CIRCUITSTATE/ESPNut-D1/Docs/Resources/ESPNut-D1-R0.1-PCB-Featured-Image-1-JPG-3-1.jpg

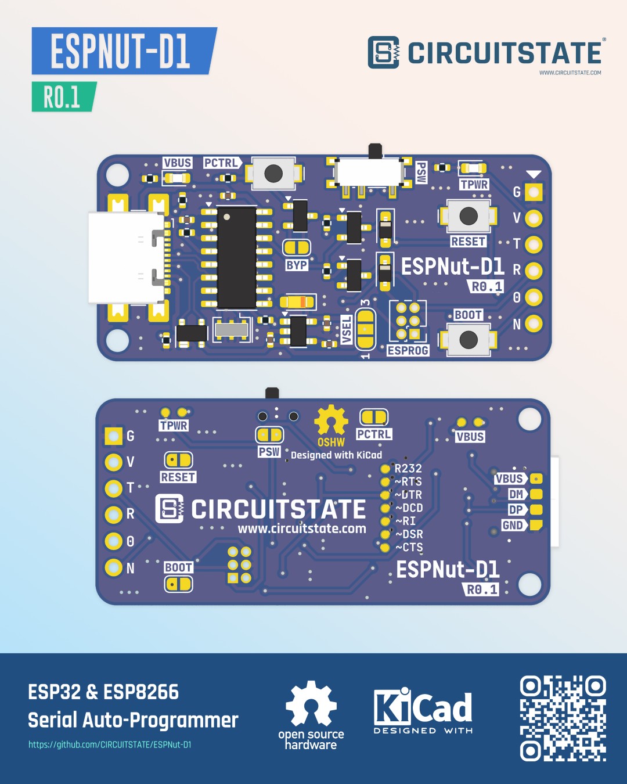
Docs/Resources/ESPNut-D1-R0.1-PCB-Featured-Image-1-JPG-3-1.jpg
