CIRCUITSTATE/ESPNut-D1/Export/R0.1/2025-04-23/Renders/ESPNut-D1-R0.1-PCB-Back-23042025-1.png

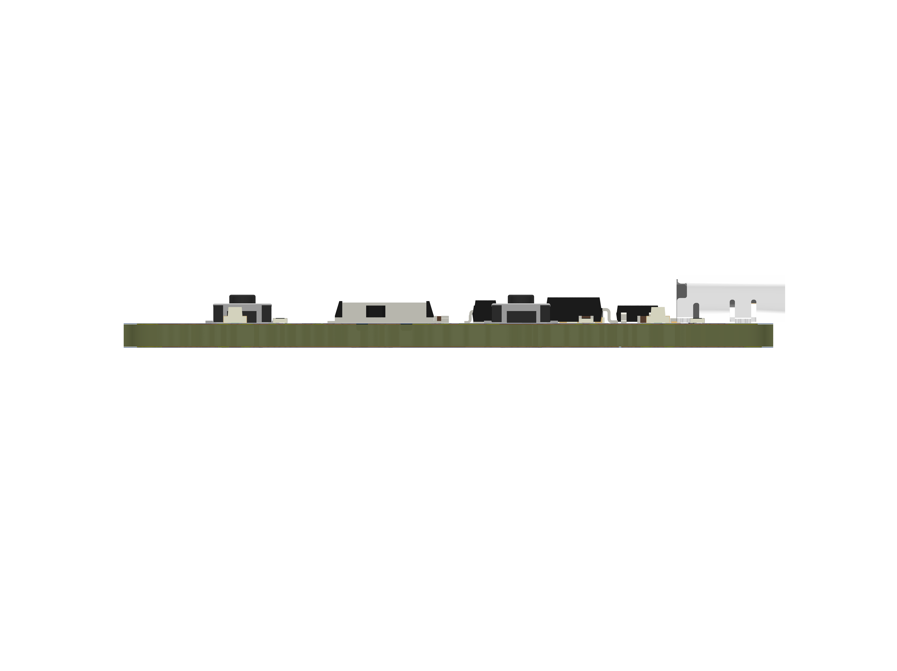
Export/R0.1/2025-04-23/Renders/ESPNut-D1-R0.1-PCB-Back-23042025-1.png
