CIRCUITSTATE/ESPNut-D1/Export/R0.3/2025-08-02/SCH/ESPNut-D1-R0.3-SCH-02082025-1_1.png

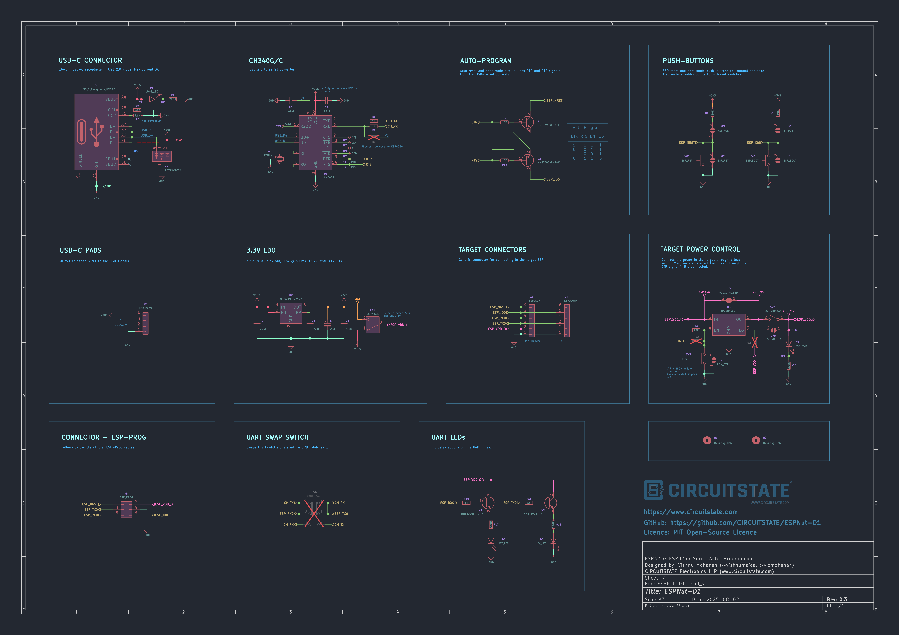
Export/R0.3/2025-08-02/SCH/ESPNut-D1-R0.3-SCH-02082025-1_1.png
