CIRCUITSTATE/ESPNut-D1/Export/R0.3/2025-10-25/Renders/ESPNut-D1-R0.3-PCB-Left-25102025-1-Cropped.png

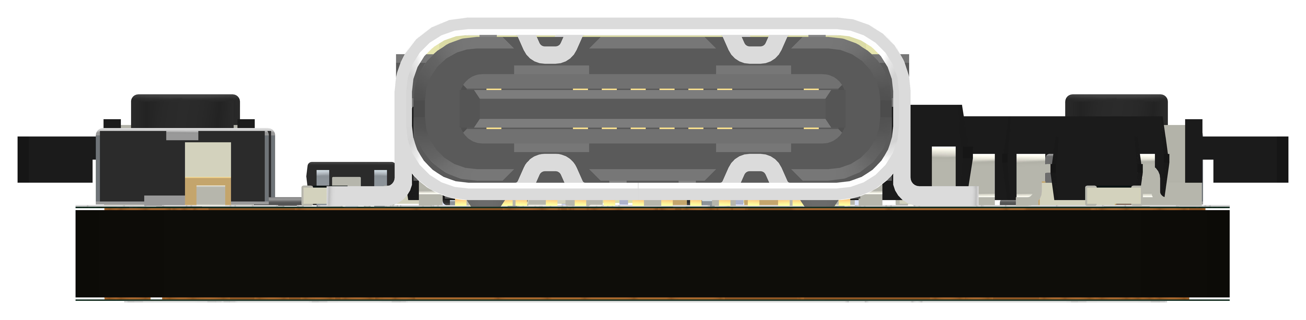
Export/R0.3/2025-10-25/Renders/ESPNut-D1-R0.3-PCB-Left-25102025-1-Cropped.png
