CIRCUITSTATE/ESPNut-D1/Export/R0.4/2025-11-07/Renders/ESPNut-D1-R0.4-PCB-Front-07112025-1-Cropped.png

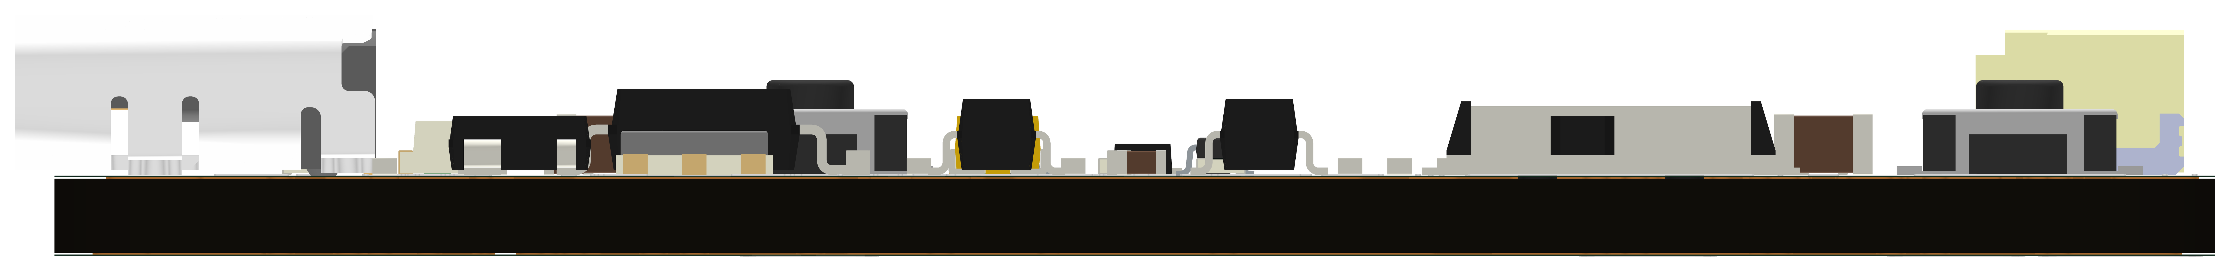
Export/R0.4/2025-11-07/Renders/ESPNut-D1-R0.4-PCB-Front-07112025-1-Cropped.png
