CIRCUITSTATE/ESPNut-D1/Export/R0.3/2025-10-23/Renders/ESPNut-D1-R0.3-PCB-Parts-Front-23102025-1.png

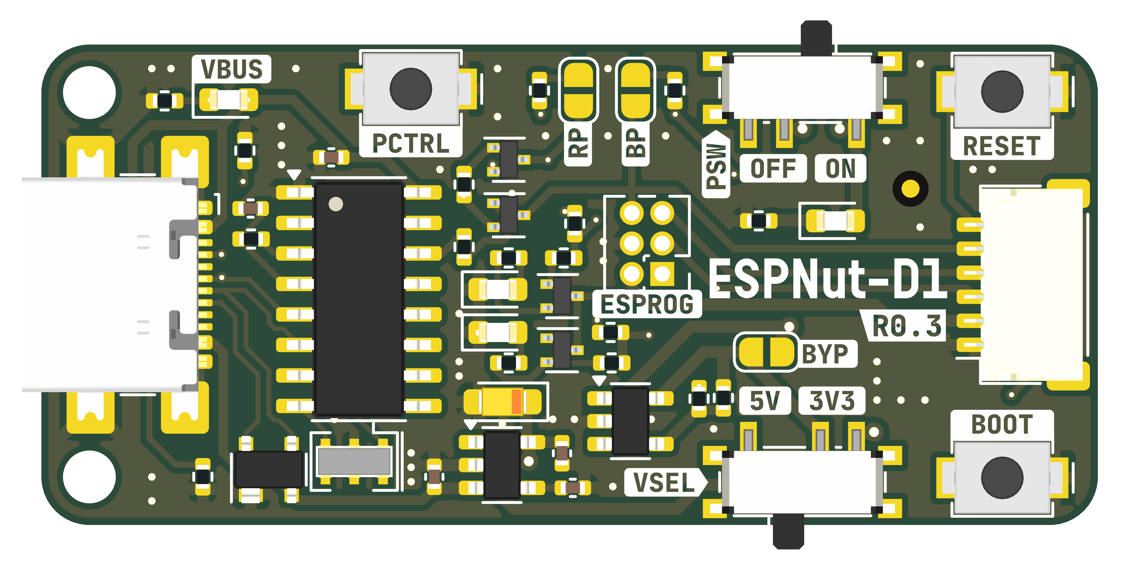
Export/R0.3/2025-10-23/Renders/ESPNut-D1-R0.3-PCB-Parts-Front-23102025-1.png
