CIRCUITSTATE/ESPNut-D1/Export/R0.4/2025-11-07/PCB/ESPNut-D1-R0.4-User_Comments.pdf

Castellated | pads: F.Mask Type | | Epsilon R | 0

0.035 mm | 1 Not specified
0 mm

4.5 | 0.02
