CIRCUITSTATE/ESPNut-D1/Export/R0.4/2025-11-07/SCH/ESPNut-D1-R0.4-SCH-07112025-1.pdf

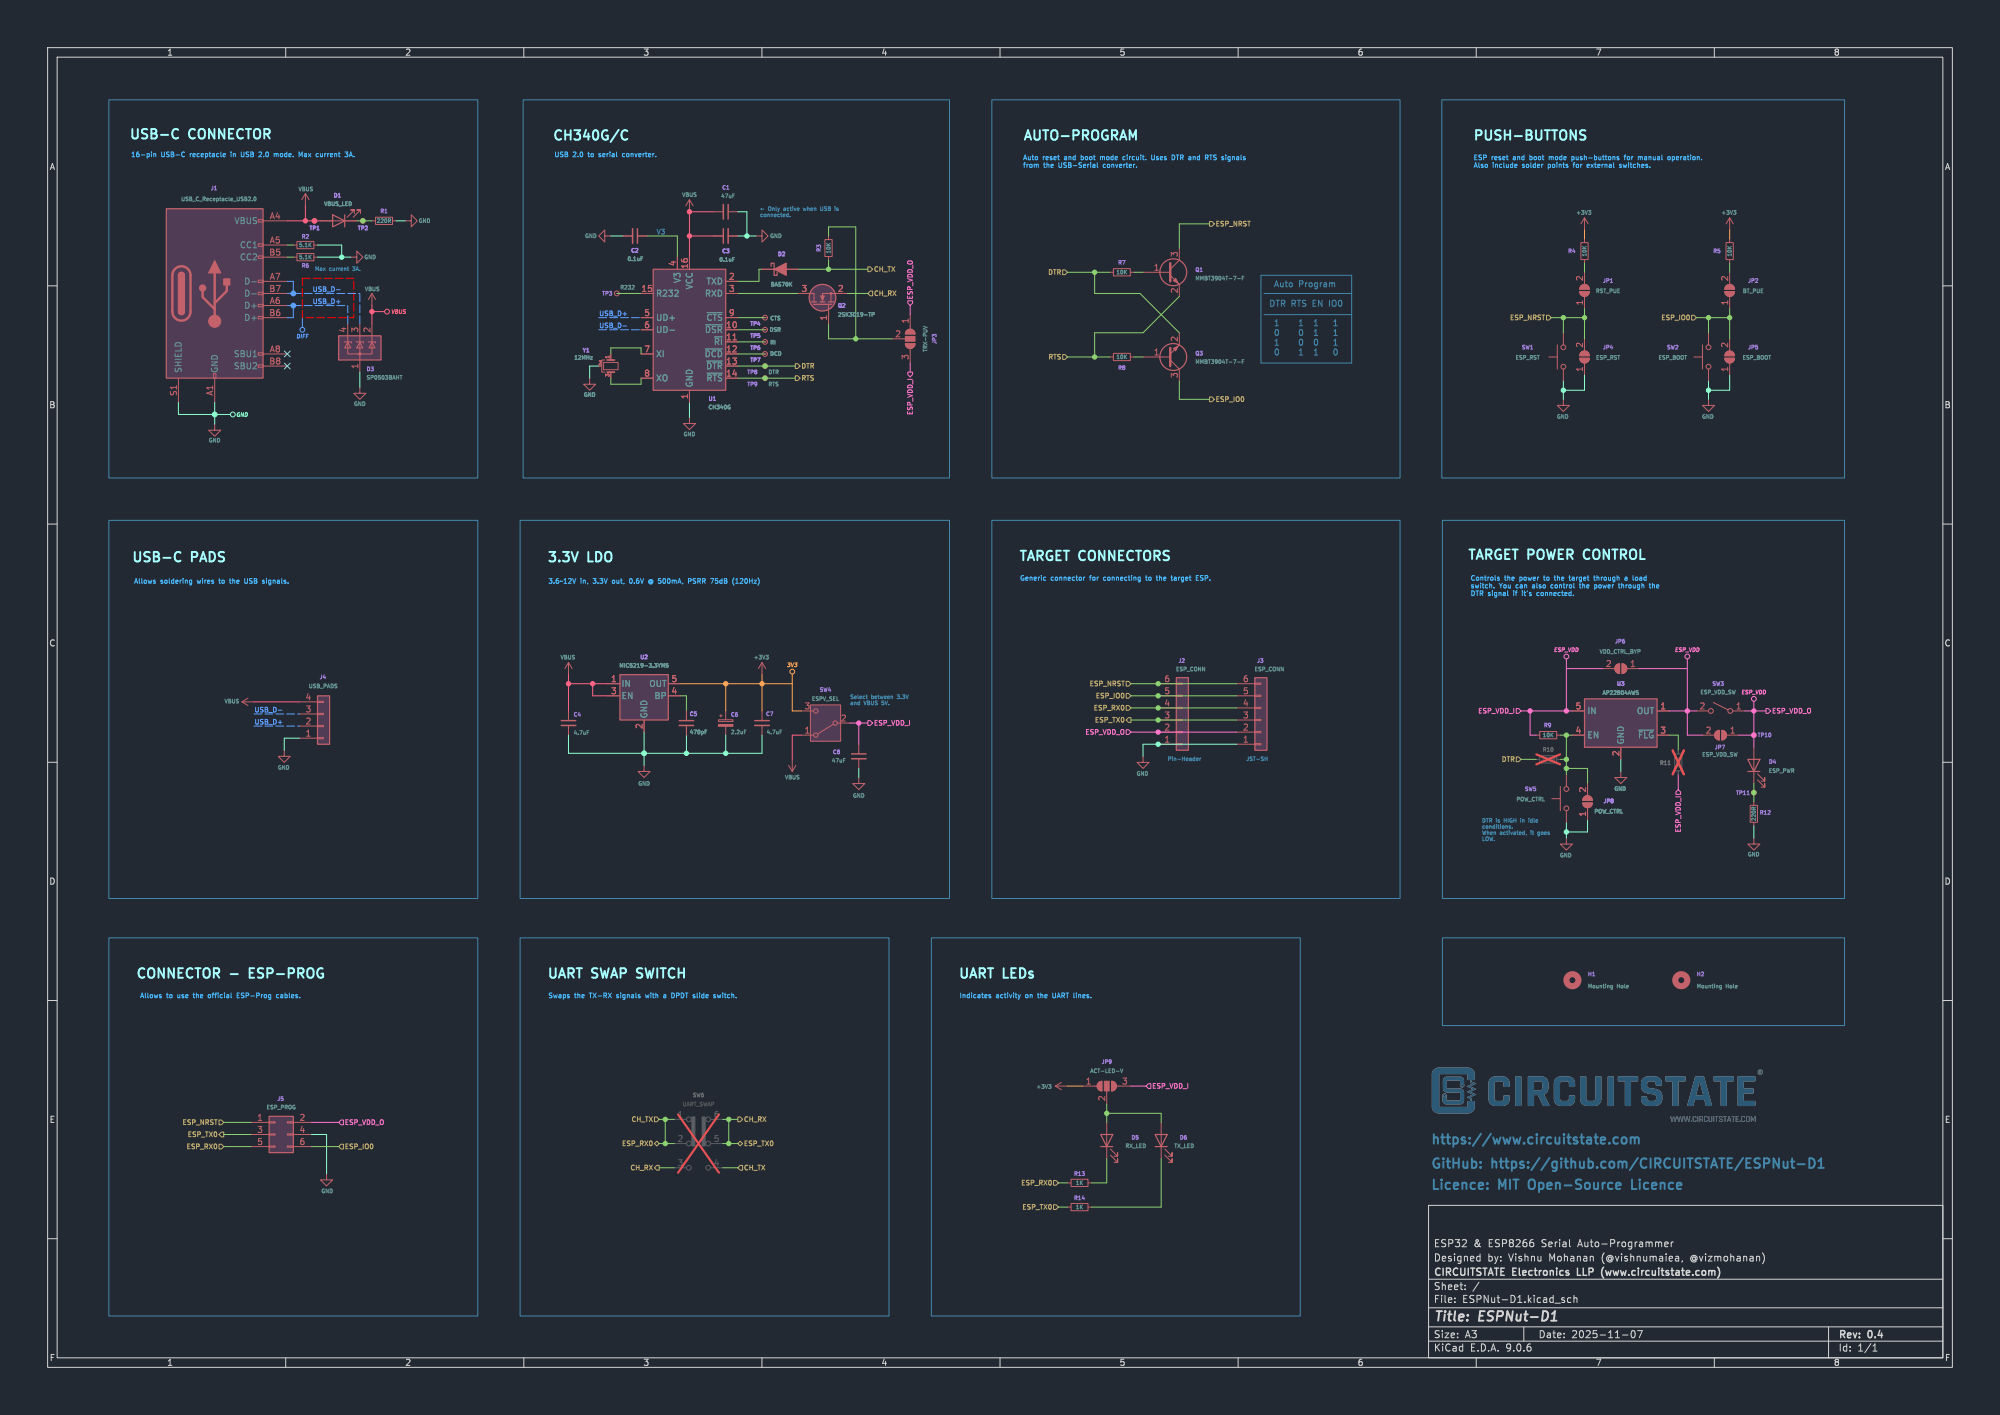
[picture p34: page 1]

þÿ!•Only active when USB is
connected.

1 TXD 2 RXD 3 ~{CTS}9 ~{DSR} 10 ~{RI} 11 ~{DCD} 12 ~{DTR} 13 ~{RTS} 14

and VBUS 5V. 3.6~12V in, 3.3V out, 0.6V @ 500mA, PSRR 75dB (120Hz)

https://www.circuitstate.com
