CIRCUITSTATE/ESPNut-D1/Export/R0.3/2025-10-25/PCB/ESPNut-D1-R0.3-PCB-PDF-All-25102025-1.pdf

D Date: 2025-08-02 KiCad; E.D.A. 9.0.5 Size: A4; Rev: 0.3; File: ESPNut-D1.kicad_pcb Sheet: CIRCUITSTATE; Electronics; LLP www.circuitstate.com; Designed; by: Vishnu; Mohanan (@vishnumaiea,; @vizmohanan) ESP32 &; ESP8266 Serial Auto-Programmer

Id: 1/1 Title: ESPNut-D1

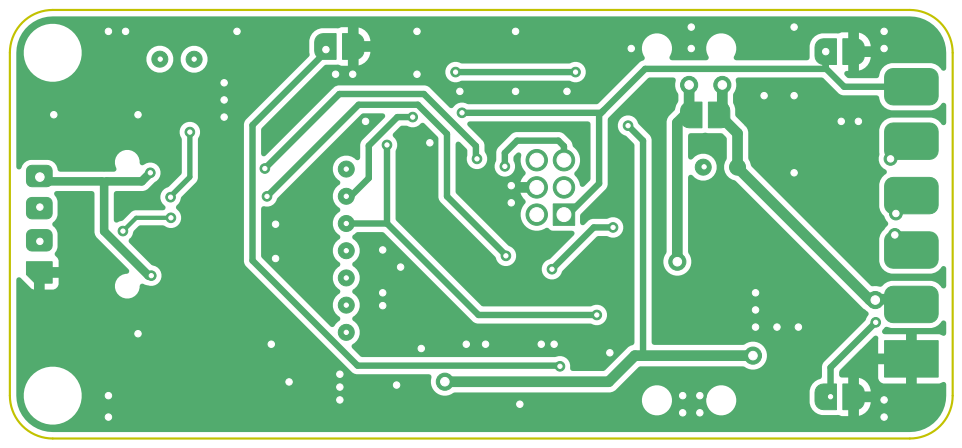
[picture p37: page 2]
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

Id: 1/1 Title: ESPNut-D1

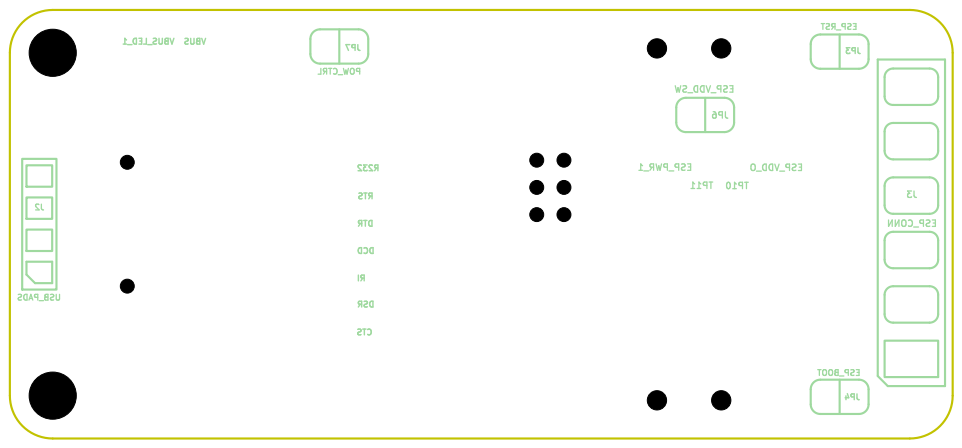
[picture p38: page 3]
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

Id: 1/1 Title: ESPNut-D1

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

Id: 1/1 Title: ESPNut-D1

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

Id: 1/1 Title: ESPNut-D1

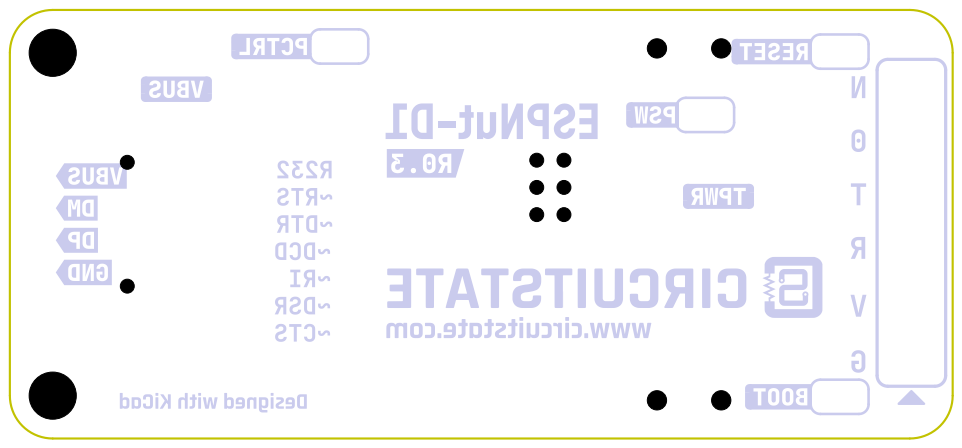
[picture p39: page 6]
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

Id: 1/1 Title: ESPNut-D1

Id: 1/1 Title: ESPNut-D1

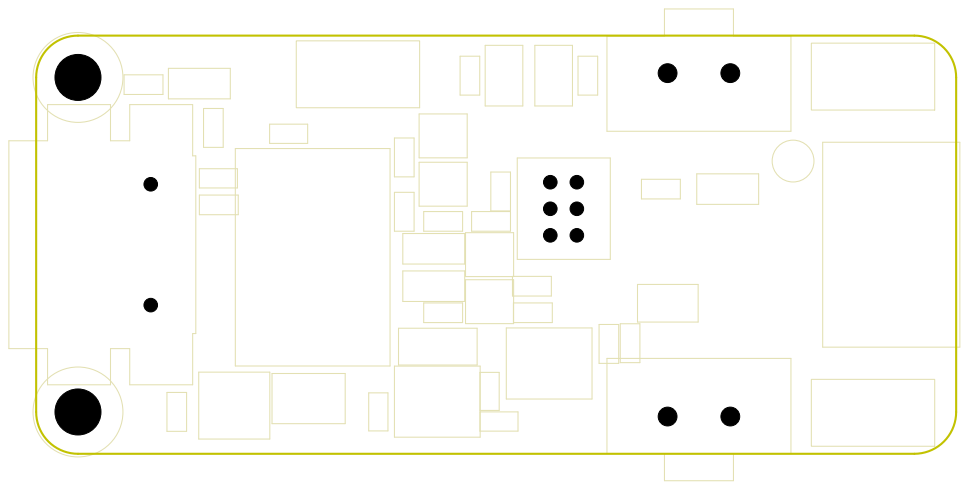
[picture p40: page 8]
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

Id: 1/1 Title: ESPNut-D1

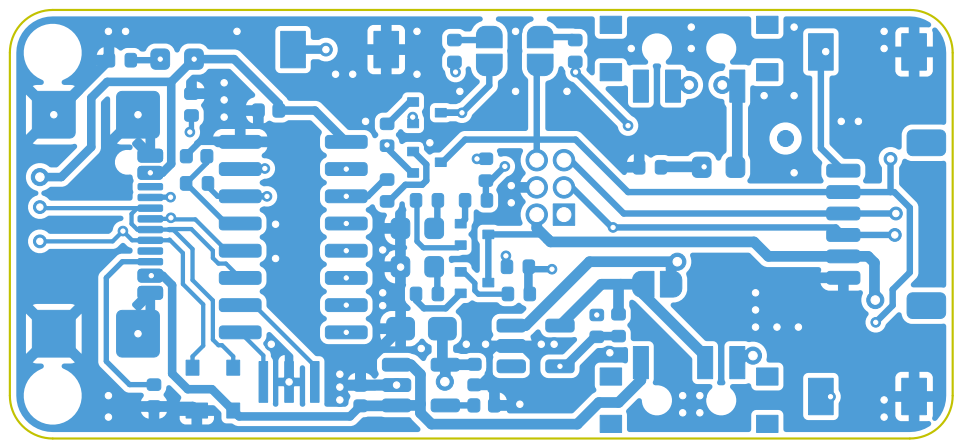
[picture p41: page 9]
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

Id: 1/1 Title: ESPNut-D1

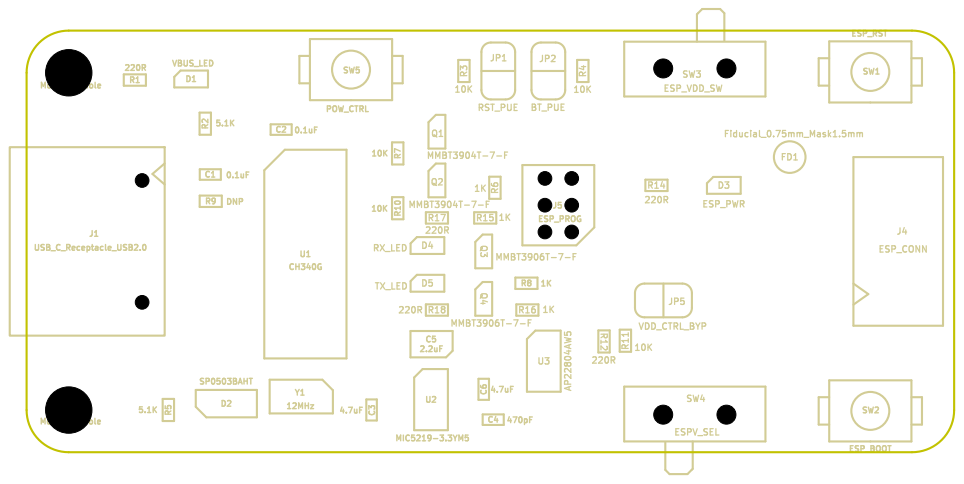
[picture p42: page 10]

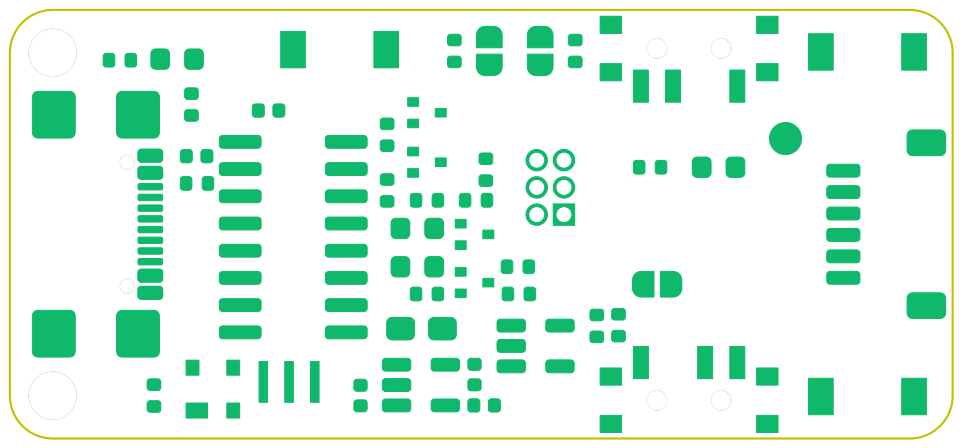
[picture p43: page 11]
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

Id: 1/1 Title: ESPNut-D1

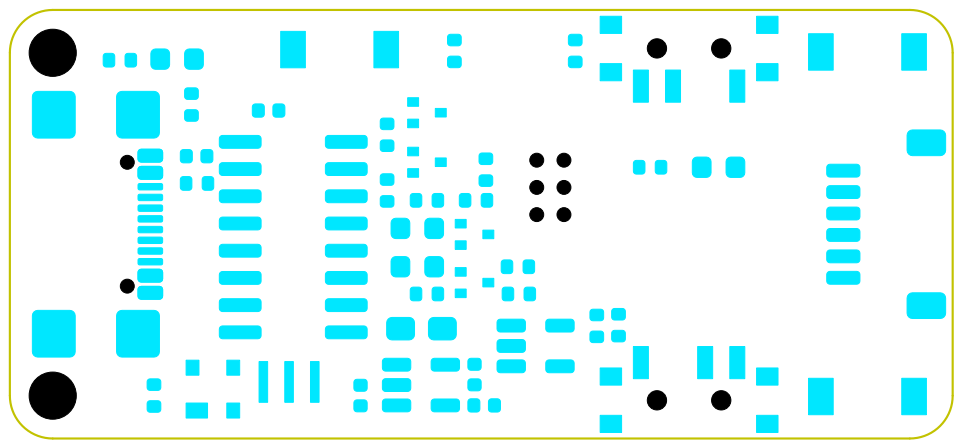
[picture p44: page 12]
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

Id: 1/1 Title: ESPNut-D1

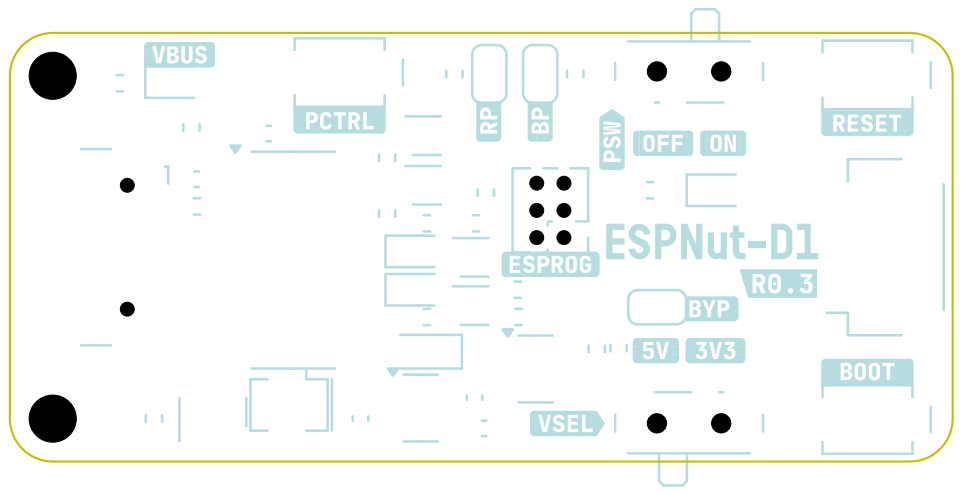
[picture p45: page 13]
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

Id: 1/1 Title: ESPNut-D1

D Date: 2025-08-02 KiCad; E.D.A. 9.0.5 Size: A4; Rev: 0.3; File: ESPNut-D1.kicad_pcb Sheet: CIRCUITSTATE; Electronics; LLP www.circuitstate.com; Designed; by: Vishnu; Mohanan (@vishnumaiea,; @vizmohanan) ESP32 &; ESP8266 Serial Auto-Programmer; BOARD CHARACTERISTICS; Board; overall; dimensions:; Not specified; Top Solder; PasteENIG; copper; F.Paste; Impedance; Control: 0.01; 0 Plated; Edge: F.Silkscreen B.Silkscreen Min track/spacing:; Thickness; (mm) Not specified; Loss Tangent Min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

Castellated | pads: F.Mask Type | | | | | | Epsilon R | 0

Layer Name Dielectric | Bottom Silk Screen Screen Bottom Solder Mask | | Not specified | 0.01 mm | | 3.3 Top Silk 3.3 1 Bottom Solder Paste 1 Not specified | 0 F.Cu

0 mm | | | 0
0 mm

0.035 mm | | 1 Not specified

4.5 | 0.02

Id: 1/1 Title: ESPNut-D1

D Date: 2025-08-02 KiCad; E.D.A. 9.0.5 Size: A4; Rev: 0.3; File: ESPNut-D1.kicad_pcb Sheet: CIRCUITSTATE; Electronics; LLP www.circuitstate.com; Designed; by: Vishnu; Mohanan (@vishnumaiea,; @vizmohanan) ESP32 &; ESP8266 Serial Auto-Programmer; PCB Edge

Id: 1/1 Title: ESPNut-D1
