CIRCUITSTATE/ESPNut-D1/Export/R0.3/2025-10-25/SCH/ESPNut-D1-R0.3-SCH-25102025-1.pdf

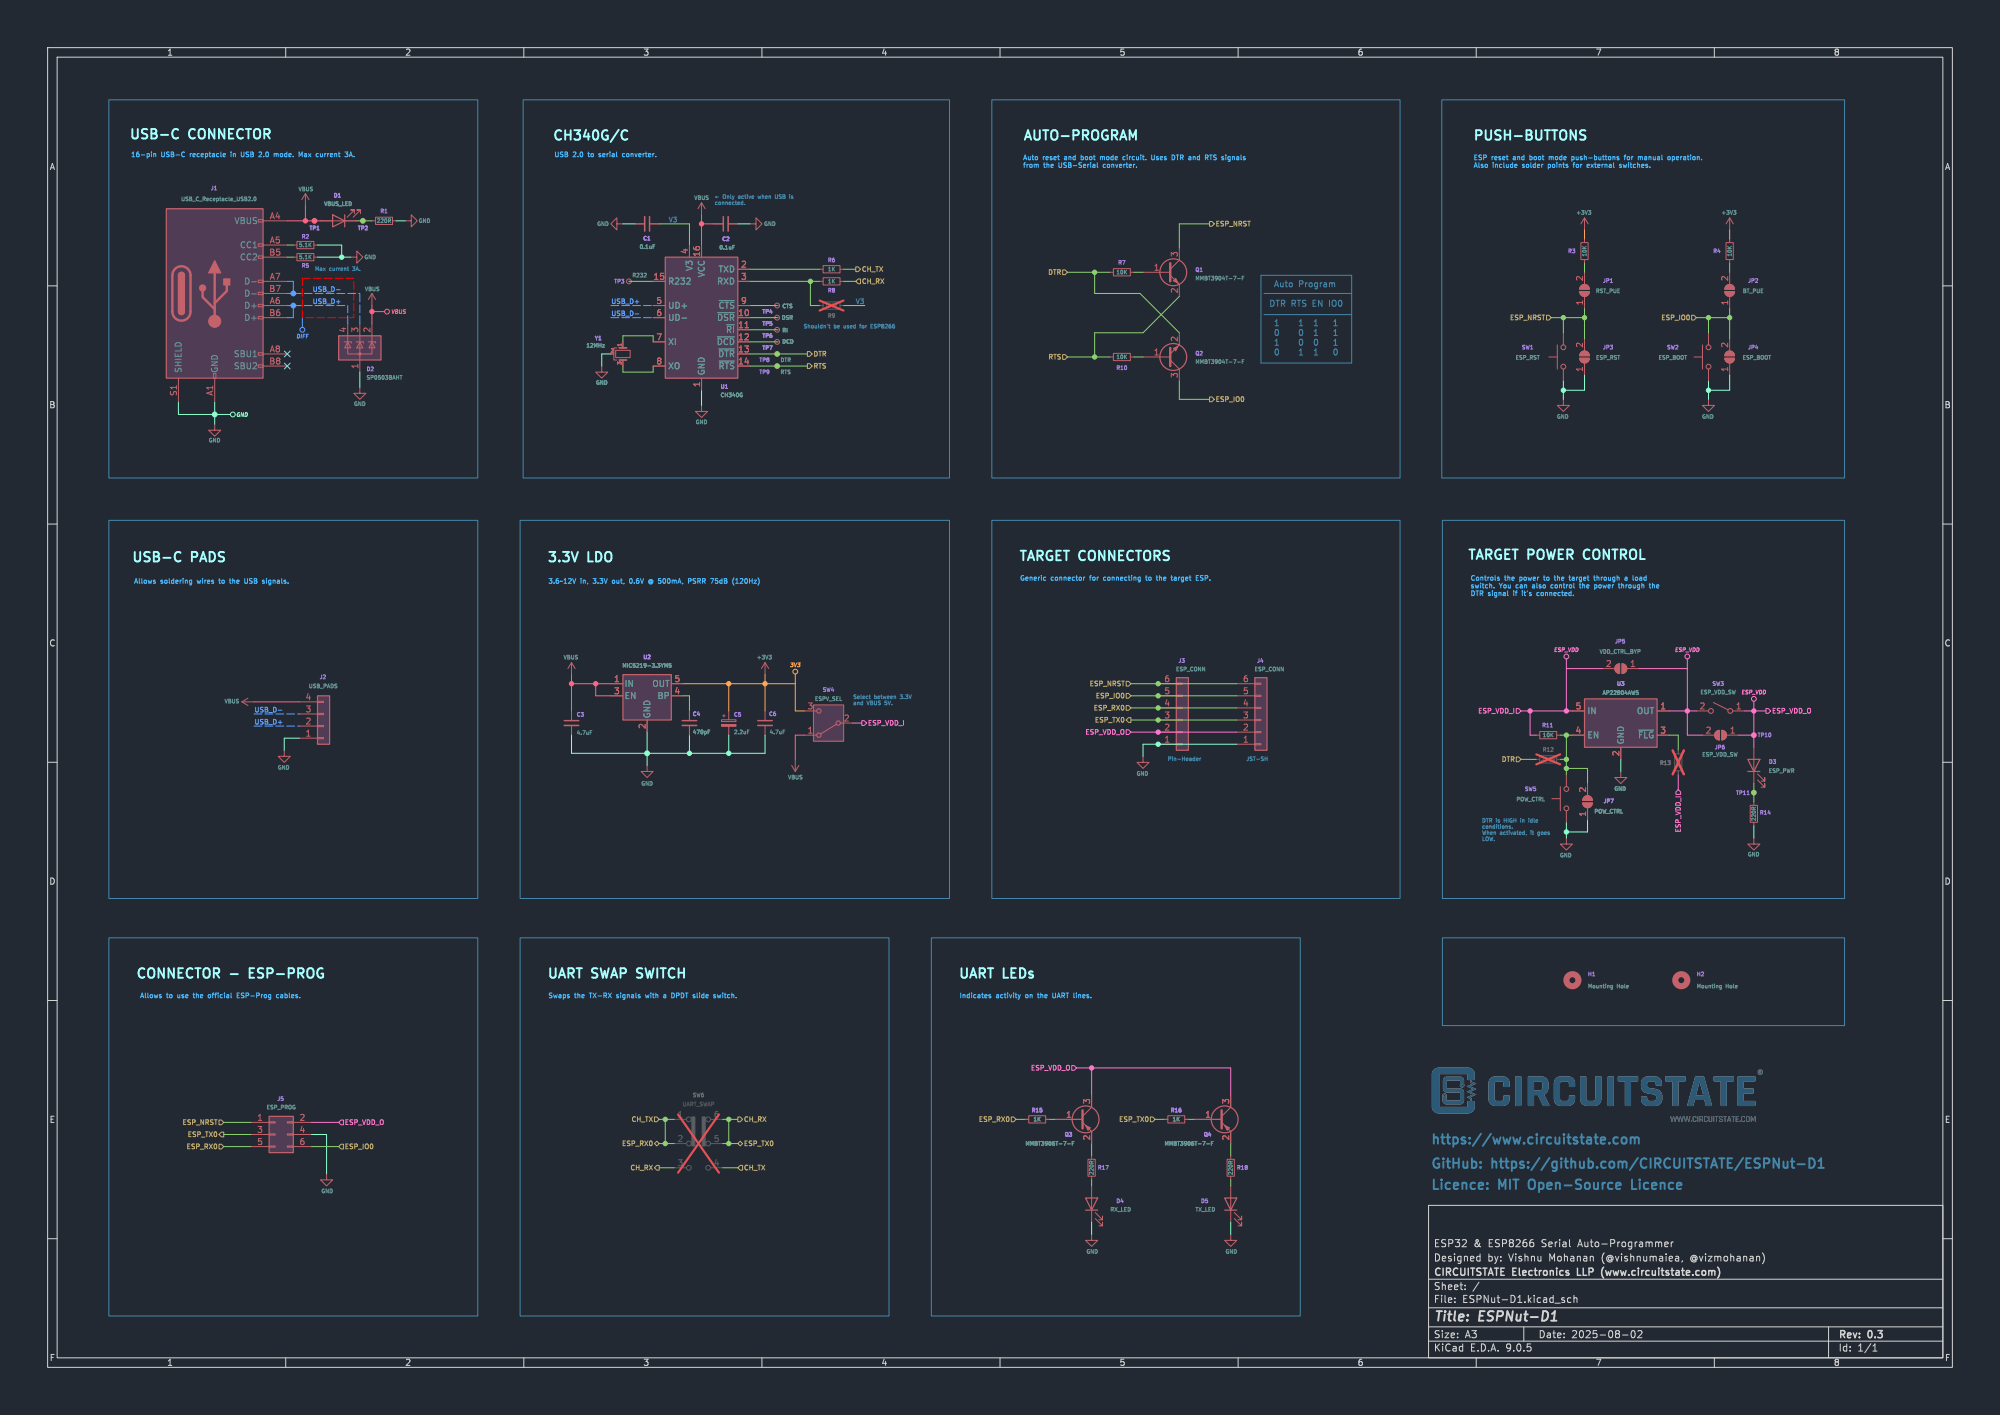
[picture p46: page 1]
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

JST-SH UART LEDs

https://www.circuitstate.com
GitHub: https://github.com/CIRCUITSTATE/ESPNut-D1
