CIRCUITSTATE/ESPNut-D1/Export/R0.1/2025-04-23/PCB/ESPNut-D1-R0.1-PCB-PDF-All-23042025-1.pdf

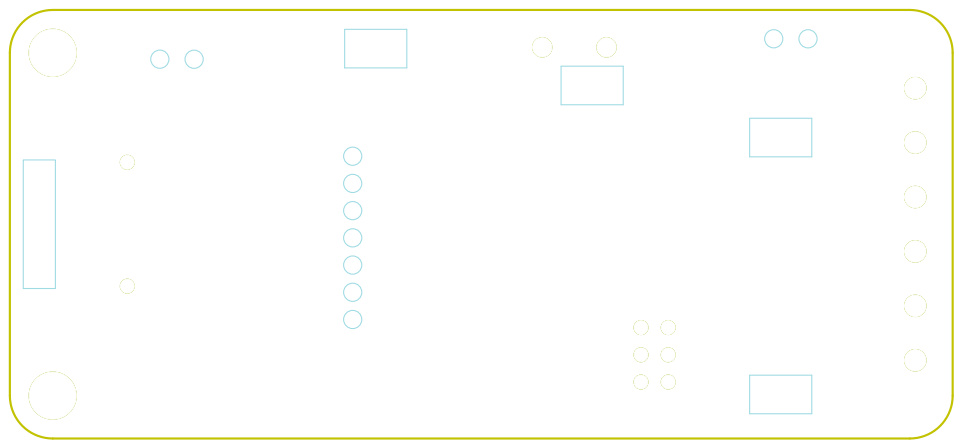
[picture p61: page 1]
D Date: 2025-04-23 KiCad; E.D.A. 9.0.1 Size: A4; Rev: 0.1; File: ESPNut-D1.kicad_pcb Sheet: CIRCUITSTATE; Electronics; LLP www.circuitstate.com; Designed; by: Vishnu; Mohanan (@vishnumaiea,; @vizmohanan) ESP32 &; ESP8266 Serial Auto-Programmer

Id: 1/1 Title: ESPNut-D1

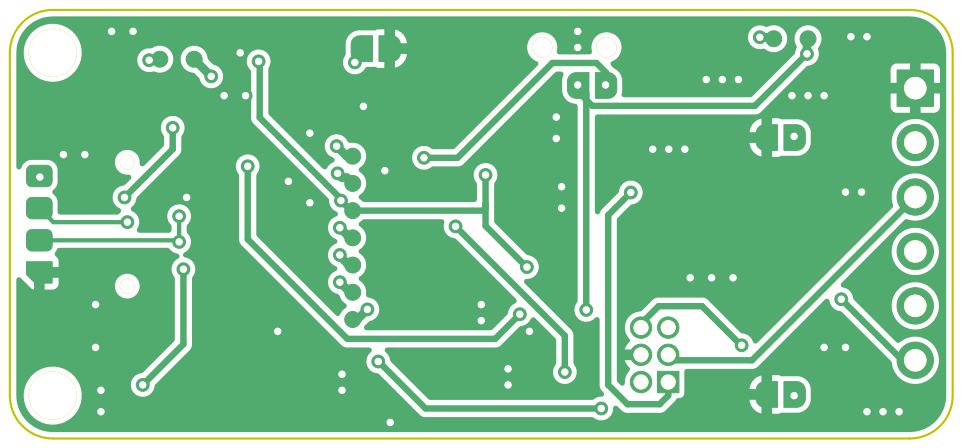
[picture p62: page 2]
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

Id: 1/1 Title: ESPNut-D1

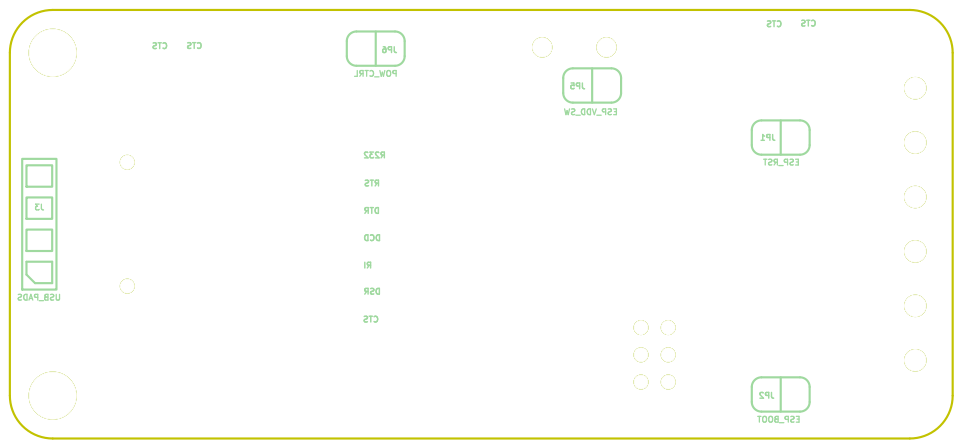
[picture p63: page 3]
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

Id: 1/1 Title: ESPNut-D1

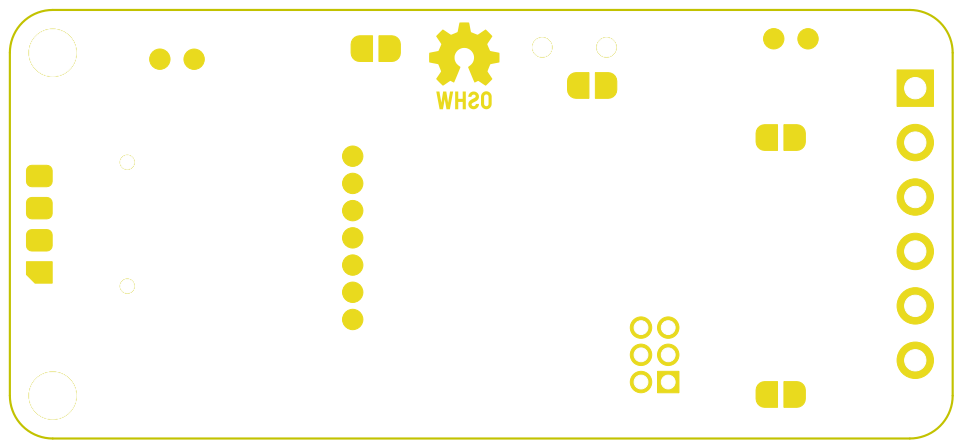
[picture p64: page 4]
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

Id: 1/1 Title: ESPNut-D1

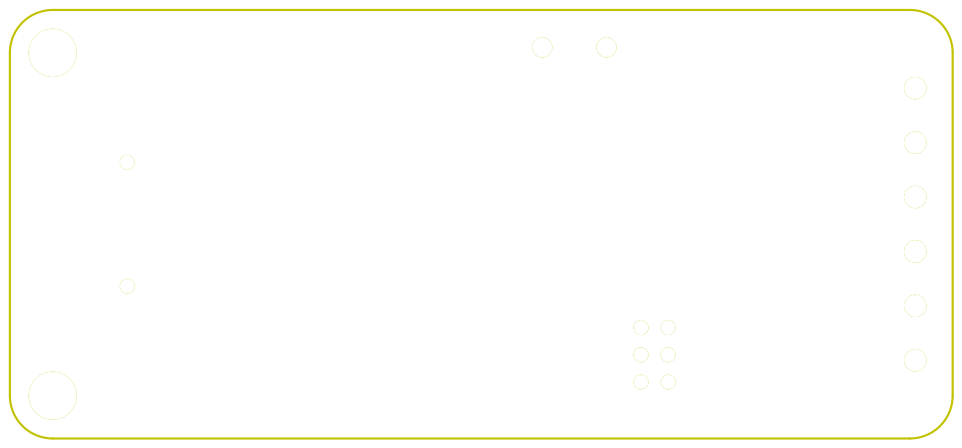
[picture p65: page 5]
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

Id: 1/1 Title: ESPNut-D1

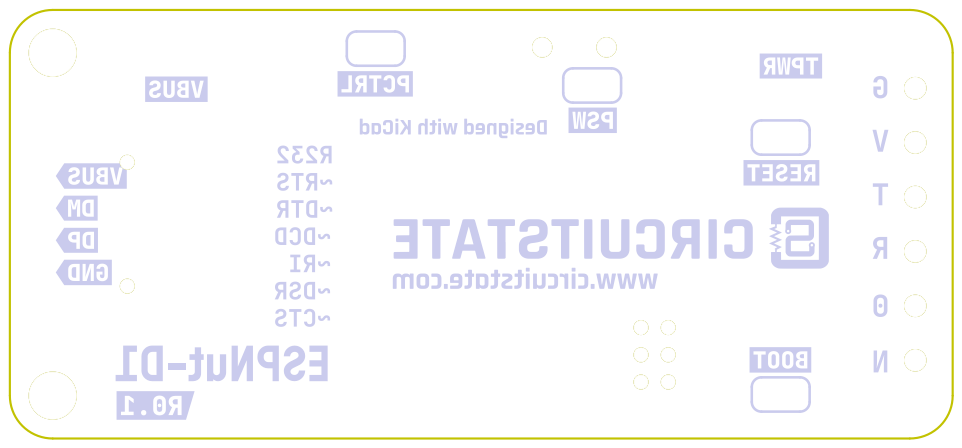
[picture p66: page 6]
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

Id: 1/1 Title: ESPNut-D1

Id: 1/1 Title: ESPNut-D1

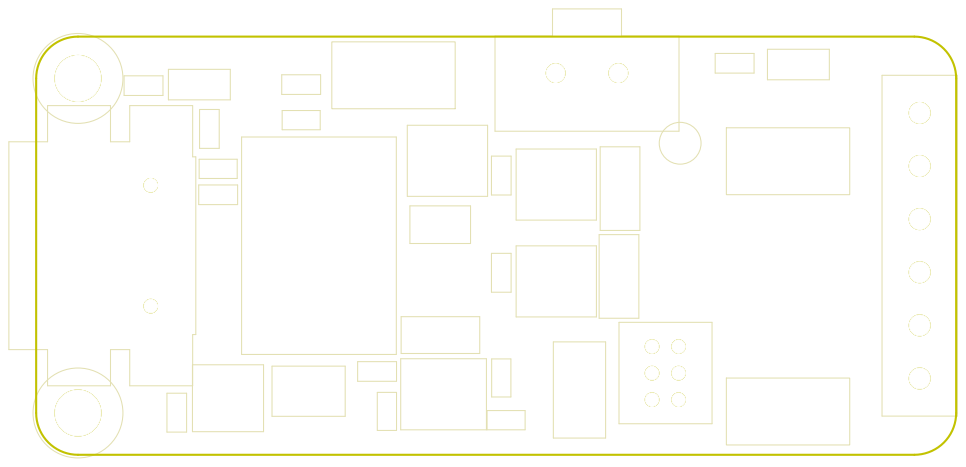
[picture p67: page 8]
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

Id: 1/1 Title: ESPNut-D1

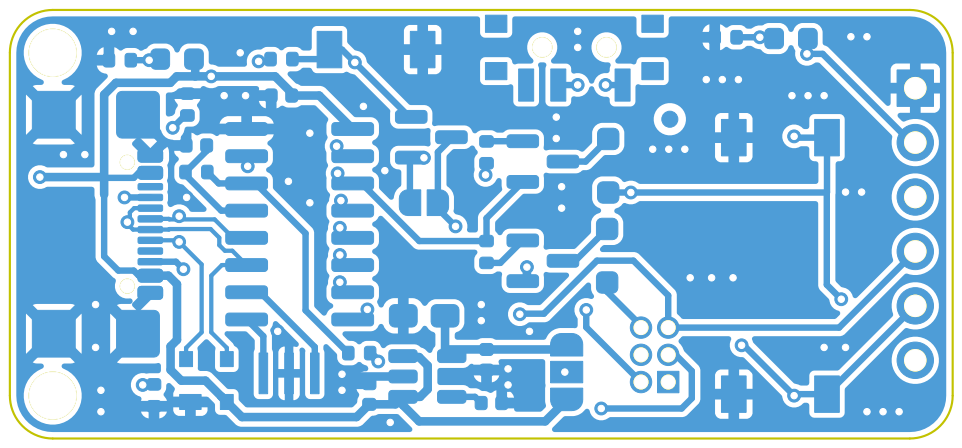
[picture p68: page 9]
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

Id: 1/1 Title: ESPNut-D1

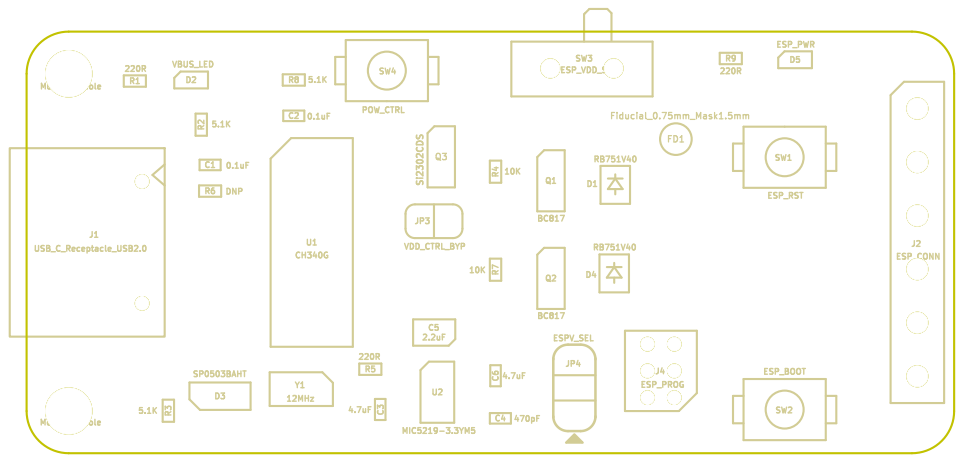
[picture p69: page 10]

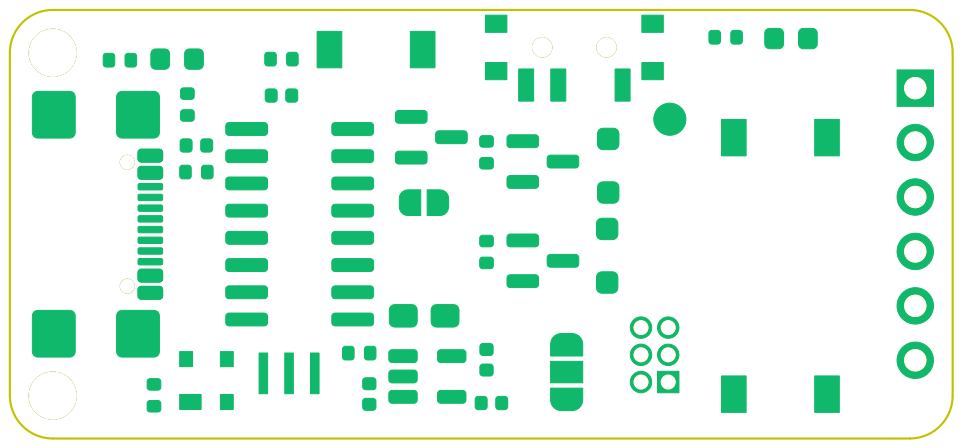
[picture p70: page 11]
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

Id: 1/1 Title: ESPNut-D1

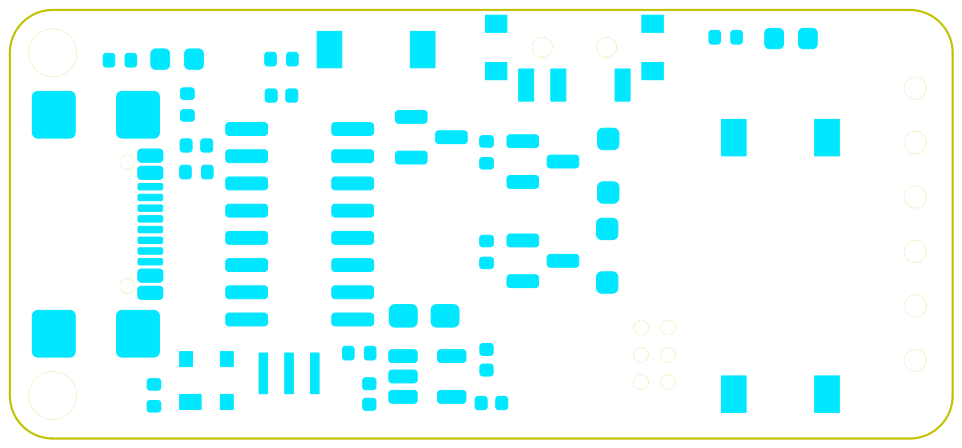
[picture p71: page 12]
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

Id: 1/1 Title: ESPNut-D1

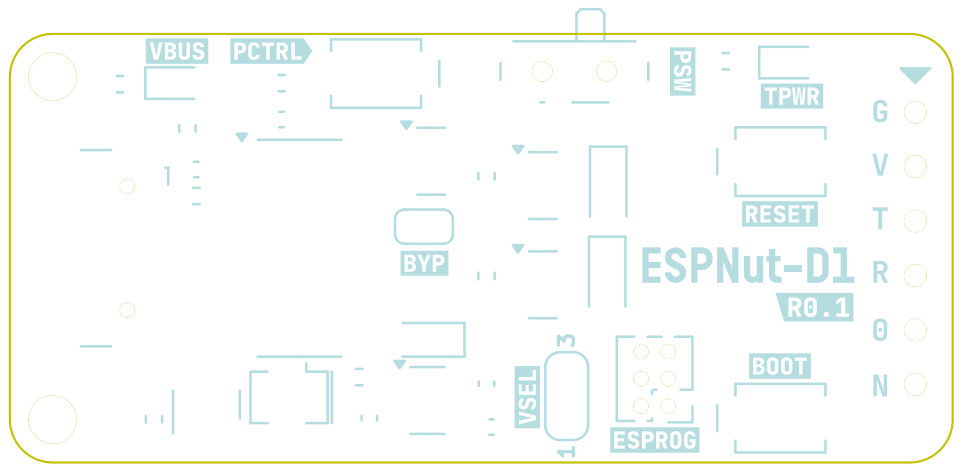
[picture p72: page 13]
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

Id: 1/1 Title: ESPNut-D1

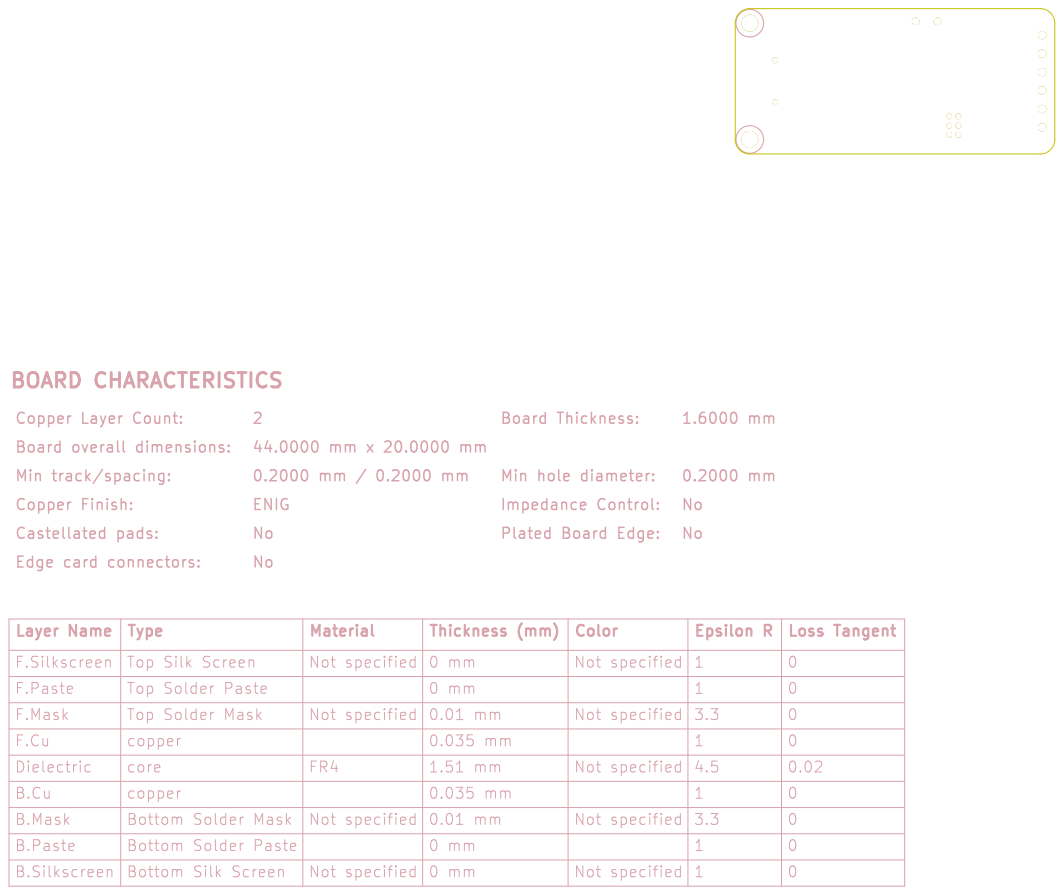
[picture p73: page 14]
D Date: 2025-04-23 KiCad; E.D.A. 9.0.1 Size: A4; Rev: 0.1; File: ESPNut-D1.kicad_pcb Sheet: CIRCUITSTATE; Electronics; LLP www.circuitstate.com; Designed; by: Vishnu; Mohanan (@vishnumaiea,; @vizmohanan) ESP32 &; ESP8266 Serial Auto-Programmer; BOARD CHARACTERISTICS; Board; overall; dimensions:; Not specified; Top Solder; PasteENIG; copper; F.Paste; Impedance; Control: 0.01; 0 Plated; Edge: F.Silkscreen B.Silkscreen Min track/spacing:; Thickness; (mm) Not specified; Loss Tangent Min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

Castellated | pads: F.Mask Type | | | | | | Epsilon R | 0

Layer Name Dielectric | Bottom Silk | Screen Screen Bottom Solder Mask | Not specified | 0.01 mm | | 3.3 Top Silk 3.3 1 Bottom Solder Paste 1 Not specified | 0 F.Cu

0 mm | | | 0
0 mm

0.035 mm | | 1 Not specified

4.5 | 0.02

Id: 1/1 Title: ESPNut-D1

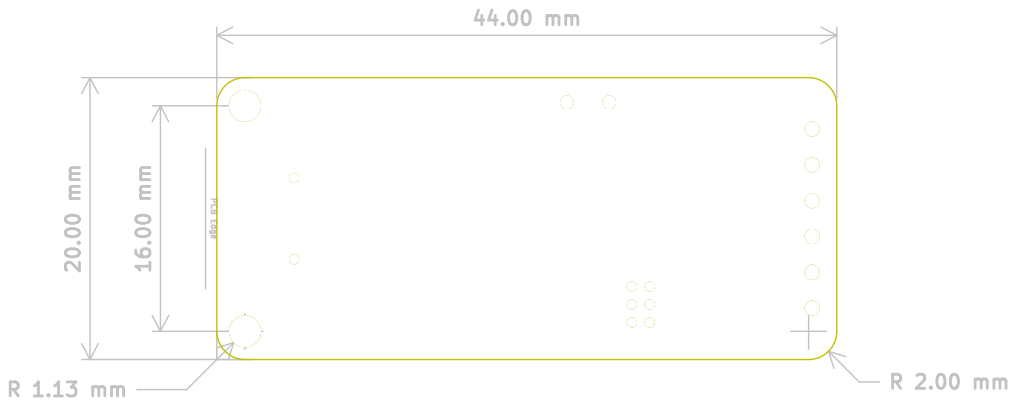
[picture p74: page 15]
D Date: 2025-04-23 KiCad; E.D.A. 9.0.1 Size: A4; Rev: 0.1; File: ESPNut-D1.kicad_pcb Sheet: CIRCUITSTATE; Electronics; LLP www.circuitstate.com; Designed; by: Vishnu; Mohanan (@vishnumaiea,; @vizmohanan) ESP32 &; ESP8266 Serial Auto-Programmer; PCB Edge

Id: 1/1 Title: ESPNut-D1
