CIRCUITSTATE/ESPNut-D1/Export/R0.1/2025-04-23/SCH/ESPNut-D1-R0.1-SCH-23042025-1.pdf

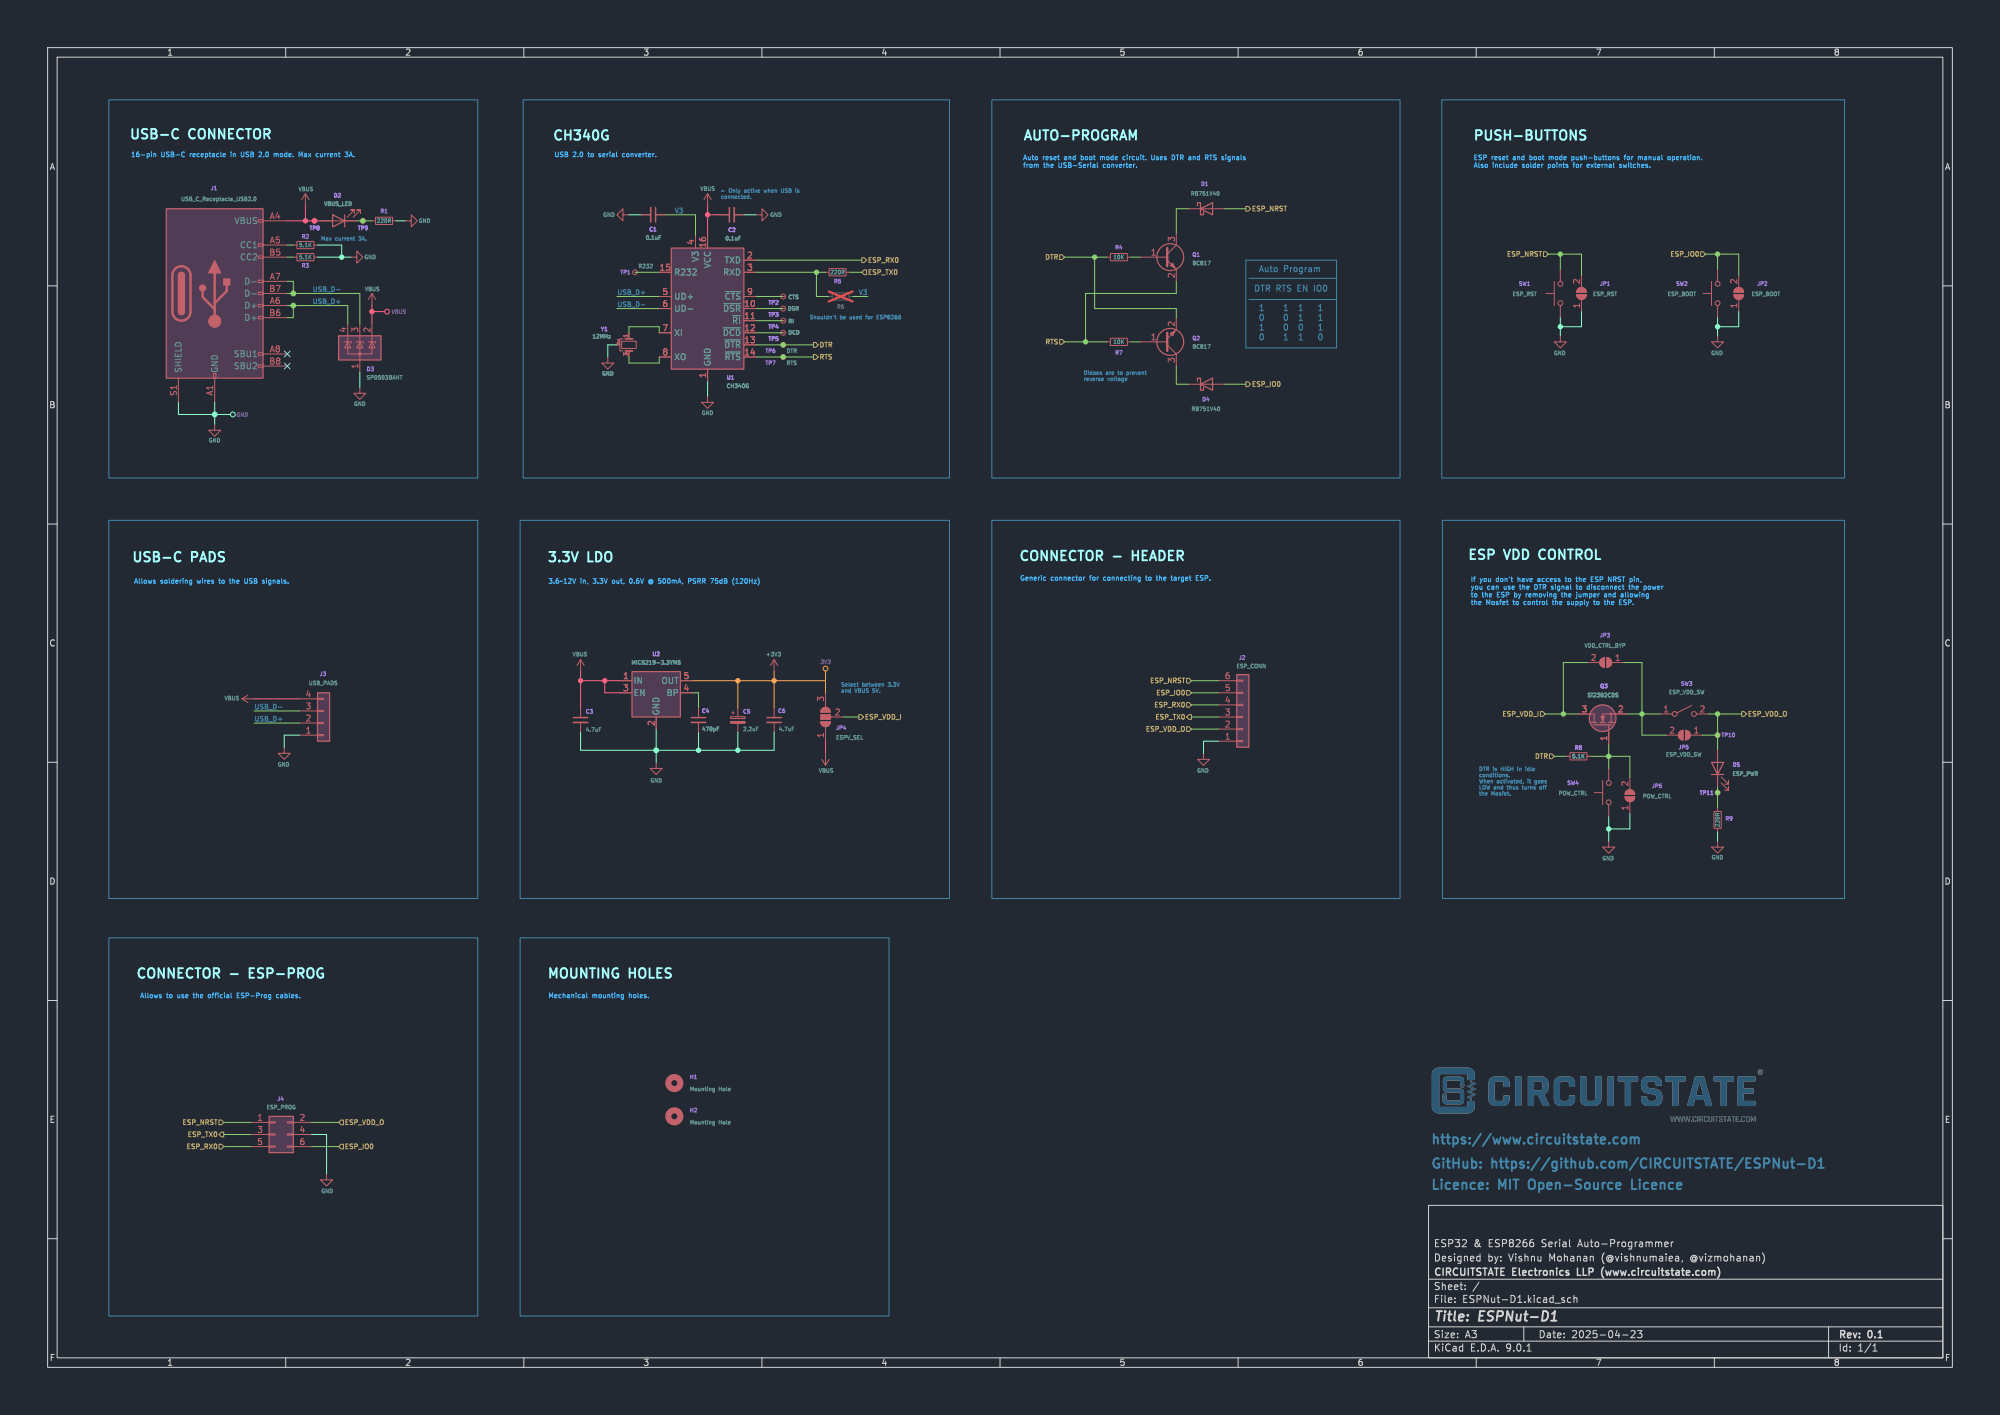
[picture p75: page 1]

þÿ!•Only active when USB is
connected.

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

Didoes are to prevent reverse voltage CONNECTOR - HEADER

https://www.circuitstate.com
GitHub: https://github.com/CIRCUITSTATE/ESPNut-D1
